nbtca/CABadge/焊接与分阶段上电检查_首板.md

# 首板焊接与分阶段上电检查

**实测结果与后续复测统一记录在 [首板测试记录.md](首板测试记录.md)。** 本文件是焊接/检查流程，下面的空表与参考范围不是最新实测状态。当前屏幕连接器问题未解决，保持拔屏；换座复核后再恢复第 4 组接屏测试。

日期：2026-09-18。针对已打板 JXBadge_EVT_20260909_c7c59dff，PCB SHA-256：c7c59dff5e6f2065a2157a81414d9d21c5cb1196a7b277656e15007753801a8d。

用户设备：万用表、USB供电；暂不接电池。下面电压是首板排查参考范围，不是实测结果或全工况产品保证。

## 先不接电池完全可以

USB-C → VBUS → D2 → VSYS → U6 → 3.3V。此路径不依赖充电芯片U5或电池。J3电池座、U5和电池支路可以最后焊。

第一轮使用正常的5V USB电源，优先独立充电头，暂不接电脑；不用快充诱骗器。普通合规快充头没有协商时通常输出5V，仍需在VBUS实际确认。充电头短路保护不能代替实验电源限流，短路仍可能损坏板子，所以每次都先做断电检查。

## 万用表使用

- 黑表笔COM，红表笔V/Ω孔，带电时直流电压档；黑表笔固定在GND。
- 不要把电流档直接跨接测试点与GND，那等于短路。当前阶段不需要使用电流档。
- 阻值/蜂鸣档只在拔掉USB、断开电池、确认电容电压已经下降后使用。
- 每加一组，检查VBUS、VSYS、3V3对GND；电容可能使读数开始较低再上升，不能只凭一声蜂鸣判短路。持续接近表笔短接电阻，例如约0～2Ω，是停下来查焊接的信号，不是所有正常板都必须高于某个统一阻值。
- 不同时供电和焊接，不带电插拔屏幕FPC。测小焊盘要防止表笔滑到邻脚，优先夹住大测试点。

## 板上测试点丝印

以下测试点名称均按板上实际丝印书写。黑表笔固定在GND，红表笔接待测点。

|板上丝印|作用|参考读数|
|---|---|---|
|3V3|系统3.3V|开机稳定约3.3V；本流程用3.20～3.40V作直流初筛|
|GND|测量参考地|0V|
|EN|主控复位使能|安装R30/C27等后，开机约3.3V，按RESET接近0V|
|D+|USB数据正|不是固定电压测试点，靠电脑枚举/下载验证|
|D-|USB数据负|同上，万用表平均电压不能验证USB通信|
|VBUS|Type-C输入|正常5V输入约4.75～5.25V|
|BAT|电池正端|目前不接电池，读数不作通过条件；接电池后为实际电池电压|
|PWR|U6电源使能|SW1开时约等于VSYS，USB供电常约4.3～5.2V；关时接近0V|

**PWR是电源芯片使能，EN是主控复位使能。USB供电且开机时，PWR接近5V是正常的；主控复位松开后，EN应接近3.3V。**

VSYS没有独立测试点，可在C22/C29的1号焊盘（非GND端）测量；先在断电状态辨认GND端。VSYS应接近VBUS减去D2正向压降，轻载下通常约4.3～5.2V，压降随负载变化，不按单一数值判故障。

## 第1组：USB输入

焊：J2、D1、D2、R18、R19、R22、C19、C20。

- R18/R19各5.1kΩ，接CC1/CC2；不能漏装，否则部分C口电源不供电。
- D1是SMF5.0A TVS，D2是DSK34肖特基，两种用途不同，不能混装。D1阴极接VBUS；D2阳极接VBUS、阴极接VSYS。
- 检查J2细脚桥连、外壳固定脚；大热容量连接器按实际焊接工具处理。

断电阻值检查通过后短时间插USB，先测VBUS，再测C22/C29的VSYS焊盘。

通过：VBUS约5V；VSYS有接近5V的电压；没有电源反复保护、冒烟、异味或明显异常升温。此时U6未装，3V3没有3.3V是正常的。

## 第2组：完整3.3V电源

拔USB后焊：U6、L3、R26、R27、R28、C22、C23、C24、C25、C26、C29、SW1。

- U6为SGM62117，先焊底部焊点难触及的芯片，再焊周围器件；不要只焊侧边可见处。
- L3必须是0.47µH功率电感，不能用24nH/2nH或普通信号电感。
- R26=560kΩ，R27=100kΩ，不得对调；R28=100kΩ。
- C22/C29各10µF，C24/C25各22µF，C23/C26各100nF。反馈和输入输出电容齐全后再通电，不能边通电边补。

检查通过后先关SW1插USB，再打开SW1。

|测量|通过参考|
|---|---|
|VBUS|约5V|
|VSYS（C22/C29非GND端）|接近VBUS减肖特基压降|
|PWR，SW1开|约等于VSYS|
|3V3，SW1开|3.20～3.40V，目标3.30V|
|PWR，SW1关|接近0V|
|3V3，SW1关|等待储能电容放电后接近0V，空载可能下降较慢|

**若3V3高于3.45V、接近5V、反复跳动，或电源芯片迅速异常发热，立即拔USB，不焊主控。**低于3.20V也先排查。U6可选测FB（R26/R27公共端）约0.50V，但不熟悉细焊盘就不探测此处。

可选负载检查：断电后在3V3与GND接100Ω、额定≥0.25W电阻，负载约33mA，再上电测3.3V。电阻发热正常，测完断电拆除。这只验证轻载，不等于整机峰值负载稳定；没有合适电阻就跳过，不拿表笔短接代替。

通过后才进入第3组。

## 第3组：主控最小系统与USB下载

焊：

- U1、U2、Y1、L1、FB1。
- R1～R9，C1～C11。
- R29、R30、C27、SW2、SW3。
- U4、R20、R21。
- AE1、L2；C12、C13按BOM保持DNP不装。

U1=ESP32-S3R8；U2=Flash；L1=24nH晶振回路电感，L2=2nH天线匹配电感，不能混装；C1/C2=24pF C0G，不能装24nF；R1～R6为0Ω连接电阻不能漏；R20/R21为22Ω。

QFN U1底部接地焊盘需焊好。用少量合适锡膏和热风/回流工艺，不能靠外围引脚焊接推断底部已连接。器件1脚以封装、芯片标记和PCB对应关系为准。

先用独立5V源检查3V3仍约3.3V；EN在复位松开后约3.3V、按RESET接近0V。可测Flash U2.8相对GND应约3.3V（芯片启用正常状态下）；不要用万用表测晶振脚并以电压判断振荡。

电源检查通过，再拔充电头，改接电脑数据线，SW1开：按住BOOT→按下并松开RESET→稍后松开BOOT，检查电脑USB设备是否出现并尝试读取芯片/Flash信息。无需已有用户固件即可进入ROM下载模式。空白Flash不能启动正常应用不是焊接失败。

通过条件：不仅是电压正确，还应稳定识别USB并成功通信；Flash容量应为16MB；8MB PSRAM需后续诊断固件检测。未识别先查数据线、CC焊接、USB细脚桥连、R20/R21、U4方向、RESET/BOOT和晶振，不急着继续焊屏幕。D+/D-不设固定直流通过电压。

## 第4组：屏幕、背光和传感器

焊：J1、U3、C14～C18、Q1、Q2、R10～R17。

包含屏幕/触摸/SC7A20去耦，共用I²C上拉，背光驱动和限流电阻。U3底部焊盘先处理，再装会遮挡操作的座子；热风不要直接长时间吹FPC塑料锁扣。R13=5.1Ω，不是5.1kΩ；不要改成0Ω。

先不插屏，上电确认3V3约3.3V且USB仍能通信。然后断电插屏，核对FPC接触面并锁紧，再上电。背光GPIO1未驱动时应关闭；在固件明确输出低时，Q1栅极约3.3V，LEDA应无持续驱动。屏幕不接时LEDA可能浮空，不以该空载电压单独判故障。

通过顺序：低亮度→纯色/渐变→触摸→姿态。只有Windows模拟器不能驱动实板，需要板端诊断固件。供电正确不等于屏幕必须自动亮。

背光导通时R13压降可用于估算电流 I=V/5.1Ω。PWM下万用表一般只能粗看平均值，不能验证导通峰值；屏幕资料典型总电流约60mA，首板不要直接满亮长期运行。

## 第5组：充电与电池路径，暂时可以不做

焊：U5、J3、Q3、Q6、Q7、R23、R31、R32、R38～R41、C21、D3、D4。

- R23原设计4.02kΩ，讨论过3.99kΩ可作为约300mA设置的替代；以实际装料记录为准。
- 如买的是UMW C725790 D+056，前次已核对引脚/封装/电流公式兼容，但手册浮充上限4.263V需结合电芯规格确认，不称为所有参数等效。
- Q3负责电池/USB供电路径。J3.1为BAT+、J3.2为GND；电池插头颜色/外形不能替代万用表极性检查。
- 无电池时LED闪烁或BAT端有电压不代表充电异常或完成。

暂不接电池时，复查3V3/VBUS即可，不能完成充电验证。

将来接电池：先拔USB，测电池自身电压和极性，再接J3；SW1开时3V3应约3.3V。再关SW1接正常5V USB，硬件允许约300mA充电。开机且GPIO38低/高阻时暂停，GPIO38高时允许；别把开机默认停充误判为焊坏。充电电流/终止电压/温升需另做实测，不能只凭指示灯放行。

## 第6组：电池电压检测，可与第5组一起补

焊：Q4、Q5、R33～R37、C28。

R36=200kΩ、R37=100kΩ，开机且接电池后BAT_ADC（C28非GND端）应约BAT/3，例如电池3.90V时约1.30V。ADC没有独立测试点，别在细引脚旁硬戳。没有电池时不能验证电池采样准确性。

## 本次最短路线

第1组USB输入 → 第2组3.3V → 第3组主控/USB下载 → 第4组显示触摸。全程可以不接电池，第5/6组留后面。

每次更换焊接组都必须拔USB；正常直流电压只是继续下一阶段的门槛，不能证明纹波、瞬态、时钟和无线都已通过。首次无任何一阶段实测结果，测完记录后再继续。

|阶段|VBUS|VSYS|PWR|3V3|EN|结果/现象|
|---|---|---|---|---|---|---|
|1 USB输入|||||||
|2 开机|||||||
|2 关机|||||||
|3 主控最小系统|||||||
|4 接屏低亮|||||||
|5 电池/充电|||||||

依据：冻结网表 `outputs/firmware-fab-netlist.xml`、实际PCB测试点网络；SGM62117手册（`hardware/datasheets/SGM62117.pdf`）与 [乐鑫硬件设计指南](https://docs.espressif.com/projects/esp-hardware-design-guidelines/zh_CN/latest/esp32s3/schematic-checklist.html)。
