nbtca/CABadge/firmware-v7/APPS.md

# CABadge v1.1.0 应用（内部 7.9.2-memory）

入口：展示页上滑 → 功能 → 应用。MC 实时地图是工具，奶蛙矿工是独立小游戏；Grok 见 [表情操作说明](GROK.md)。

## MC 实时地图

直接读取 https://bluemap.orangedog.nbtca.space:8001 的 BlueMap 地形瓦片与在线玩家 JSON。
吧唧需要连接可访问互联网的 Wi-Fi；仅开启吧唧自己的热点不提供互联网。

- 单指拖动平移；底部减号放大视野、加号缩小视野；出生点按钮复位。
- 顶部维度按钮切换主世界、下界、末地；玩家用蓝点标示，上次请求完成后约 10 秒再次获取；并非严格每 10 秒到达。
- 支持 6 档比例、BlueMap 3 级低分辨率地形，不运行网页中的 3D 渲染器。
- 当前服务器 501×1002 PNG 的上半部是颜色，下半部是高度/光照数据；只使用颜色生成俯视图。
- 使用 128×128 RGB565 瓦片缓存，最多 9 张；这是为内存预算选择的地形精度，不是网页原画质。
- 网络下载与 PNG 解码在独立低优先级任务执行；手指拖动当前图片，松开后异步补齐地图。
- HTTPS 校验服务器证书；联网后 SNTP 校时。失败显示错误，不降级关闭证书验证。
- 单点触摸使用按钮缩放；未实现双指缩放。当前维度默认中心：主世界 (48,96)，其余 (0,0)。

## 奶蛙矿工

源仓库：https://github.com/66970010-boop/frog-miner 。源网页标题为“奶蛙工厂”；按用户请求在应用入口使用“奶蛙矿工”。
原素材与源码归原作者，本项目为用户要求的嵌入式改编。下载来源、SHA256 见 `ui/app_assets/source.json`。

- 点击矿区或“出钩 / 收回”：出钩；钩子下降期间再点可提前收回。
- 保留 45 秒关卡、分数目标、三档难度、移动大蛙/困难档移动出钩点、不同物品回收速度、稀有蛙与 47 格图鉴。
- 支持暂停、继续、过关、下一关、失败重试；最高分和图鉴保存在 NVS。
- 原网页音效未移植：当前硬件没有音频输出。大型剧情/粒子动画用简短状态反馈替代。
- 图鉴目前按编号显示，画面按 360×360 圆屏重排；不是网页 800×600 画面的逐像素复刻。

## 内存与所有权

当前 HTTP 输入缓冲 **16 KiB**；压缩 PNG 最大接收限制仍为 1 MiB，该上限不是常驻分配。BlueMap 专用 Pngle 增量解码，解压窗口与扫描线位于 PSRAM，采样上半部颜色直接写 128×128 RGB565；不保存整张 501×1002 RGBA 或完整 IDAT。继续消费完整 PNG 校验 CRC/结束状态。
9 张瓦片合计 294,912 B；单张输出 259,200 B，GUI 交接可同时保留新旧图。HTTP/TLS 清理后再分配输出；取消与退出等待实际 worker cleanup，避免与大转场重叠。其他图片业务的 LodePNG/JPEG 未替换。
工作任务栈 8 KiB，首次使用才创建；离开地图取消过期请求并释放瓦片/输出。
结果由 GUI 任务接收和更换图像源；工作任务不修改 LVGL 对象或图片缓存。
游戏素材是 Flash 中的常量；游戏逻辑和页面对象不持续读写壁纸分区。

## 验证

矿工历史规则测试保存在 Git 历史中；当前复刻树保留正式玩法源码与原始资源，不自动运行旧应用探针。
当前瓦片回归：`python firmware-v7/test_map_stream.py`，验证碎片输入、RGB565 采样、CRC 和截断拒绝；可传入保存的真实瓦片 PNG。旧 LodePNG 解码检查已随过时工具清理，历史记录仍可追溯。

本版实板一次基本检查：地图四瓦片、一玩家、error0，Grok 进出及返回主页；矿工未在 R63 新增完整玩法回归。来源见根首板测试记录 R63。旧自动导航工具已移除。新包在 `outputs/cabadge-v7.9.2-memory`，旧应用发布包仅保留历史含义。
软件计数不是屏幕扫描帧率或触摸手感证据；实体拖动、按键命中和目视撕裂由用户检查。
