nbtca/CABadge/firmware-v7/GROK.md

> 本功能保留于 v1.1.0 / 7.9.2-memory，以下原始实现和测试段落保留当时版本含义。当前内存/显示架构见 [固件说明](README.md)，本体继续实时绘制。

# Grok 表情球

基于 tycoding/grok-ball 的 MIT 眼形数据改编，入口为“功能 → 应用 → Grok”。版权与下载源码哈希保存在 `ui/grok_source/`。BlueMap 优化继续搁置。

## 操作

- 进入后全屏显示球面，默认隐藏操作控件。
- 手指按住并移动：眼睛跟随；超过 8 像素判为拖动，松手不切换表情。
- 轻点：下一种表情。
- 原地长按：显示/隐藏操作控件；左右按钮选择表情，“配色”切换自动配色/深色，“返回”回到应用列表。
- 60 秒没有交互进入闭眼表情；这不是硬件息屏。系统息屏后停止绘制，醒来恢复；退出应用释放图像缓存。

## 实现与边界

保留 25 组左右各 48 点轮廓及 32 种状态的眼形池、配色、过渡时间和眨眼间隔。采用 C 原生轮廓插值、球面横向压缩、双子行抗锯齿扫描转换；不运行 JS、SVG 引擎或浏览器。移除了自旋、彩带、撒花。复杂原版序列和附加特效并非逐项复刻，32 种是状态数据数量，不代表完整移植 32 套网页特效。

所有绘制与触摸在原有 GUI 任务中执行，复用 33ms 应用定时器，无新增任务。图像源在 GUI 顺序执行期间更新；LCD DMA 使用原有独立 LVGL 绘图缓冲，不直接读取此图像源。退出先删除图像对象，再清图像缓存并释放内存。

7.6.1 初版为 256×256 图像、约 240 像素球体；用户实屏指出未铺满。7.6.2 改为 360×360、半径 180 球面，图像固定 (0,0)，消除外围留白。眼睛/眨眼仅使新旧轮廓包围区域失效，球面换色才全图失效。底图和输出各 259,200 B，总计 518,400 B，明确分配 PSRAM。字体新增字形仅加入实际使用的 18 号字库。

## 验证

`python -B firmware-v7/ui/generate_grok.py` 验证原始轮廓与状态索引并生成常量表。

`ui/grok_render_test.c` 直接使用生产扫描转换代码，检查 32 配色、25 眼形和 5 个越界偏移的缓冲哨兵；不运行模拟器。编译时使用本地 Zig、`-O2 -DLV_CONF_INCLUDE_SIMPLE -Ifirmware-v7 -Ifirmware-v7/vendor/lvgl-9.4.0`。

`python -B firmware-v7/grok_probe.py` 在 COM3 上检查版本、进入/退出、息屏无重绘、唤醒恢复、PSRAM 回收及图库保持；不会修改电脑 WLAN。实际手指体验、全屏贴边及撕裂由用户实屏验收。LCD 提交计数不是面板扫描频率。

发布包为 `outputs/cabadge-v7-grok-full-20260923`。需要回退时仅烧录 `outputs/cabadge-v7-apps-20260923/firmware.bin` 到 0x10000，不擦除壁纸和 NVS。
