nbtca/CABadge/docs/THIRD_PARTY.md

# 第三方来源

本项目 MIT 只覆盖有权授予的原创代码；第三方组件及素材遵循各自许可。

- LVGL 9.4.0：MIT，上游 https://github.com/lvgl/lvgl，构建下载，未整库入库。
- ESP-IDF / Espressif Adapter 与 LCD 驱动：保留组件各自许可，版本见 dependencies.lock。
- Pngle / miniz：随 firmware-v7/usb_screen/device/src/pngle/ 保存许可证、来源及源码哈希；https://github.com/kikuchan/pngle。
- Grok 表情轮廓：来源 https://github.com/tycoding/grok-ball；原 MIT LICENSE 与来源记录保留在 ui/grok_source/。
- 奶蛙矿工规则/素材：来源 https://github.com/66970010-boop/frog-miner；来源及哈希保留在 ui/app_assets/source.json。当前工程未保存可确认的独立素材授权文本，不声称这些角色素材受本项目 MIT 授权。
- 字体：Noto Sans SC / SIL OFL，由 setup_deps.py 获取原 OFL 文本。其他既有图片与协会标识保留原权利归属。
