nbtca/CABadge/firmware-v7/usb_screen/device/src/panel_init.h

// Generated from supplier W180TE010I 360x360 initial code; verify with verify_display.py.
static const struct { uint8_t command, count; uint16_t delay_ms; uint8_t data[14]; } panel_init[] = {
    {0xF0, 1, 0, {0x28}},
    {0xF2, 1, 0, {0x28}},
    {0x73, 1, 0, {0xF0}},
    {0x7C, 1, 0, {0xD1}},
    {0x83, 1, 0, {0xE0}},
    {0x84, 1, 0, {0x61}},
    {0xF2, 1, 0, {0x82}},
    {0xF0, 1, 0, {0x00}},
    {0xF0, 1, 0, {0x01}},
    {0xF1, 1, 0, {0x01}},
    {0xB0, 1, 0, {0x5E}},
    {0xB1, 1, 0, {0x55}},
    {0xB2, 1, 0, {0x24}},
    {0xB3, 1, 0, {0x01}},
    {0xB4, 1, 0, {0x87}},
    {0xB5, 1, 0, {0x44}},
    {0xB6, 1, 0, {0x8B}},
    {0xB7, 1, 0, {0x40}},
    {0xB8, 1, 0, {0x86}},
    {0xB9, 1, 0, {0x15}},
    {0xBA, 1, 0, {0x00}},
    {0xBB, 1, 0, {0x08}},
    {0xBC, 1, 0, {0x08}},
    {0xBD, 1, 0, {0x00}},
    {0xBE, 1, 0, {0x00}},
    {0xBF, 1, 0, {0x07}},
    {0xC0, 1, 0, {0x80}},
    {0xC1, 1, 0, {0x10}},
    {0xC2, 1, 0, {0x37}},
    {0xC3, 1, 0, {0x80}},
    {0xC4, 1, 0, {0x10}},
    {0xC5, 1, 0, {0x37}},
    {0xC6, 1, 0, {0xA9}},
    {0xC7, 1, 0, {0x41}},
    {0xC8, 1, 0, {0x01}},
    {0xC9, 1, 0, {0xA9}},
    {0xCA, 1, 0, {0x41}},
    {0xCB, 1, 0, {0x01}},
    {0xCC, 1, 0, {0x7F}},
    {0xCD, 1, 0, {0x7F}},
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
};
